hollop90/Remote-Sensor-Node/Solar Data/1W Panel MPPT.png

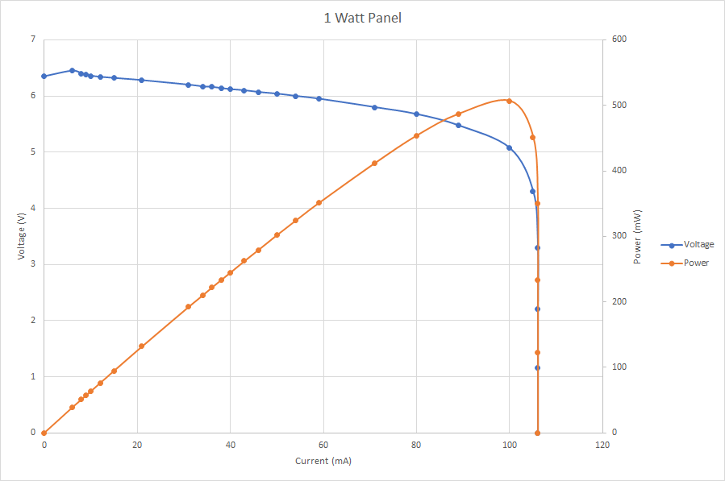
Solar Data/1W Panel MPPT.png
