hollop90/Remote-Sensor-Node/Solar Data/3W Panel MPPT.png

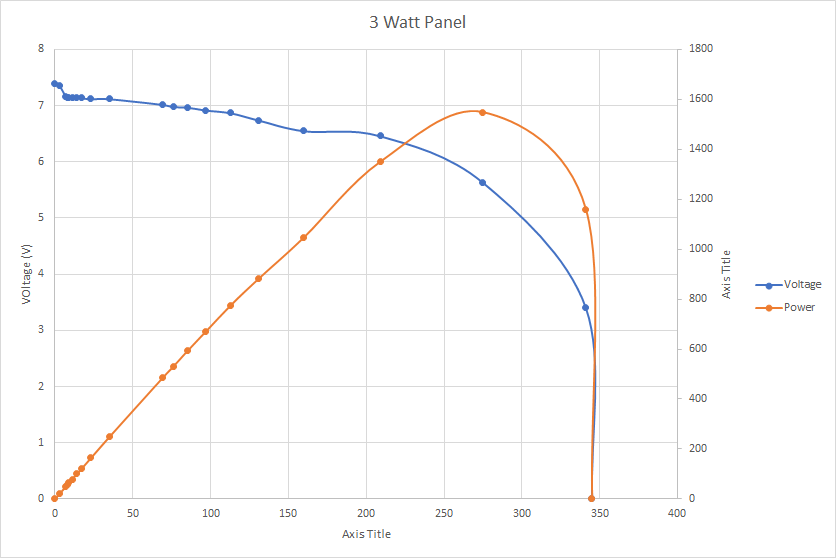
Solar Data/3W Panel MPPT.png
