hollop90/Remote-Sensor-Node/Images/MPPT Test Setup (1).jpg

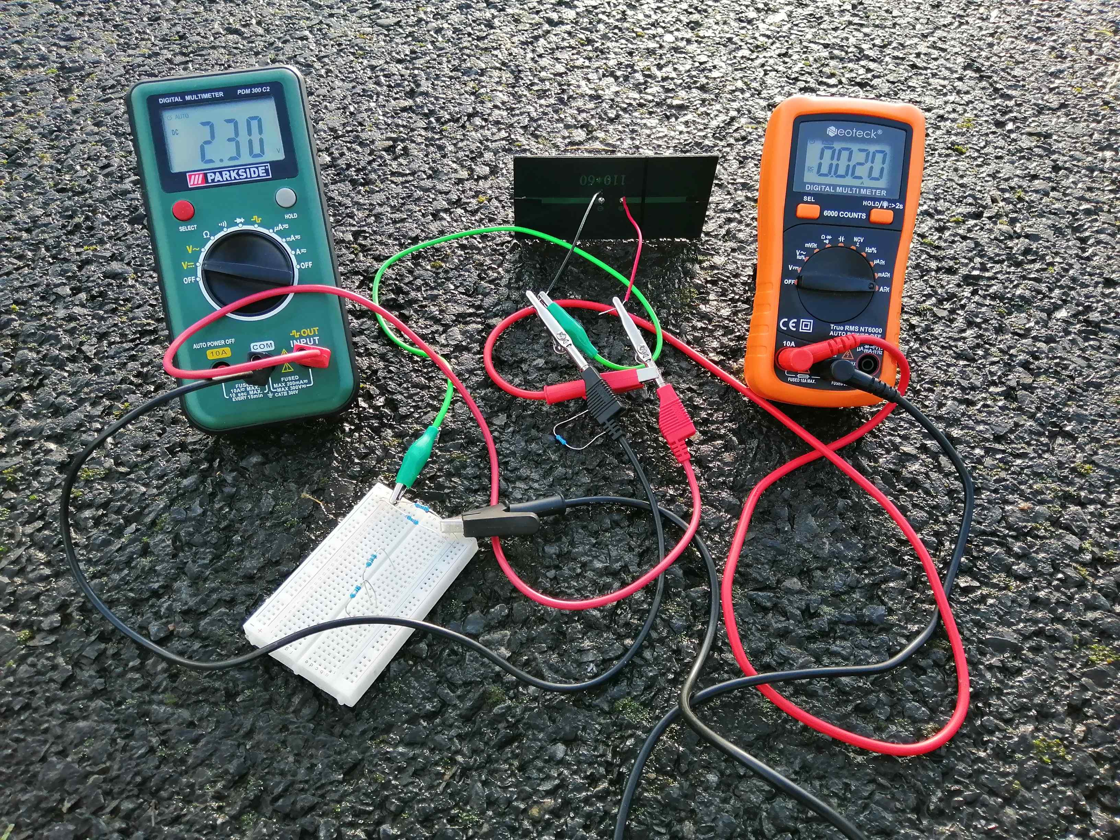
Images/MPPT Test Setup (1).jpg
