hollop90/Remote-Sensor-Node/Solar Data/MPPT Results.png

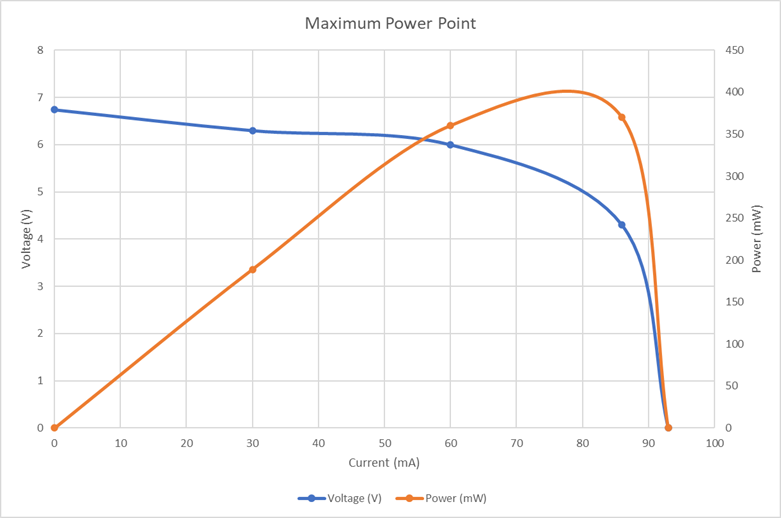
Solar Data/MPPT Results.png
